EugenieChabenat/ATC_communication_interface/CAD_files/STEP_files/Support_1.step

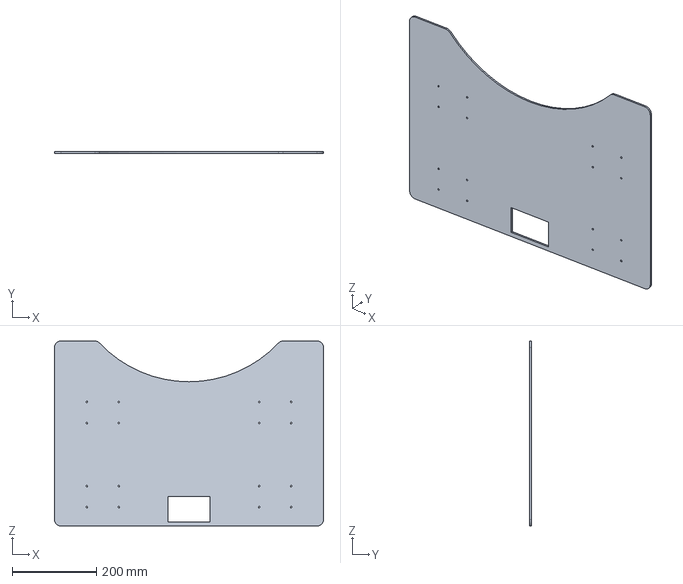
[picture p15: CAD file, 2021-06-13]
CAD_files/STEP_files/Support_1.step
640.0 x 4.00 x 440.0 mm
